Kennystflr/Lightning-speaker/projectLS v1.2.png

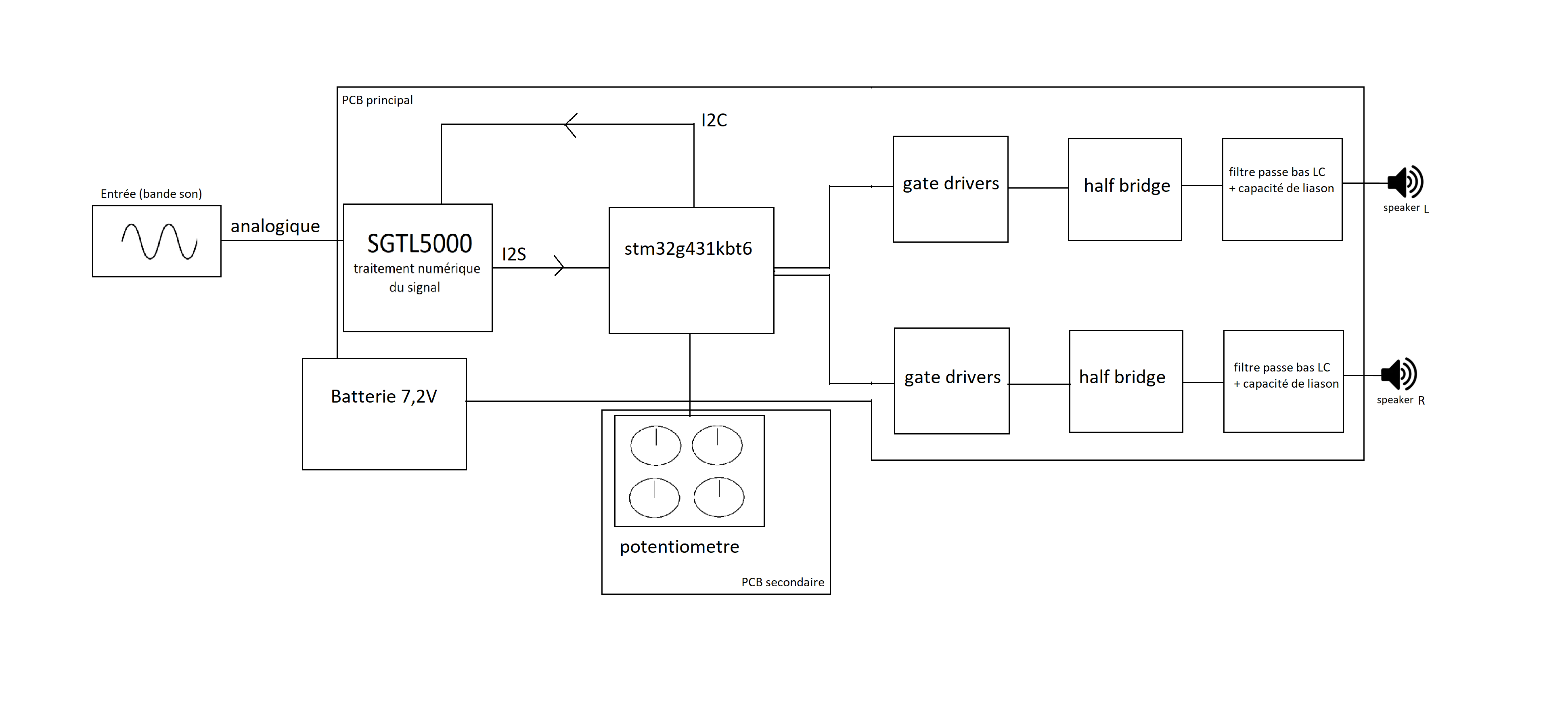
projectLS v1.2.png
